bigbadevilaussie-hue/Fan-Mate/WebServer.cpp

#include "WebServer.h"
#include "WiFiManager.h"
#include "FanController.h"
#include "Logging.h"
#include "Settings.h"
#include "OpalClient.h"
#include "AutoBoost.h"
#include "Config.h"
#include "WebPage.h"
#include "SerialBuffer.h"

#include <WebServer.h>
#include <ESPmDNS.h>
#include <LittleFS.h>
#include <Update.h>
#include <ArduinoJson.h>
#include <time.h>
#include <sys/time.h>

extern int  kill_get_state();
extern void kill_request_clear();
extern void kill_request_auto();

static WebServer server(HTTP_PORT);

extern volatile bool otaInProgress;
static bool otaStarted = false;
static unsigned long host_last_ms = 0;

static void note_host() { host_last_ms = millis(); }

static void handle_serial_page() {
    String html = R"rawliteral(
<!DOCTYPE html><html><head><meta charset="utf-8">
<title>Fan-Mate Serial</title>
<style>
html,body{margin:0;padding:0;height:100%;overflow:hidden}
body{font-family:ui-monospace,monospace;background:#181825;color:#cdd6f4;font-size:13px}
#log{background:#181825;padding:6px;height:100%;overflow-y:auto;white-space:pre-wrap;word-break:break-all;box-sizing:border-box}
</style>
<script>
function refresh(){
  fetch('/serial-raw')
    .then(r=>r.text())
    .then(t=>{
      const el=document.getElementById('log');
      const at_bottom = el.scrollHeight - el.scrollTop - el.clientHeight < 50;
      el.textContent = t;
      if(at_bottom) el.scrollTop = el.scrollHeight;
    });
}
setInterval(refresh, 2000);
window.onload = refresh;
</script>
</head><body>
<div id="log">loading...</div>
</body></html>
)rawliteral";
    server.send(200, "text/html", html);
}

static void handle_serial_raw() {
    server.send(200, "text/plain", get_serial_dump());
}

static void handle_root() {
    note_host();
    server.send_P(200, "text/html", INDEX_HTML);
}

static void handle_status() {
    note_host();
    extern float currentTemp;
    extern int   fanPct;
    extern int   fanRPM;
    extern int   alertState;
    extern bool  phonePresent;
    extern float lastNetKbps;
    extern bool  fan_stall_active();

    String json = "{";
    json += "\"fw\":\"" + String(FAN_MATE_VERSION) + "\",";
    json += "\"uptime\":" + String(millis() / 1000) + ",";
    json += "\"ip\":\"" + wifi_ip() + "\",";
    json += "\"rssi\":" + String(wifi_rssi()) + ",";
    json += "\"ssid\":\"" + wifi_ssid_connected() + "\",";
    json += "\"temp\":" + String(currentTemp, 2) + ",";
    json += "\"fan\":" + String(fanPct) + ",";
    json += "\"rpm\":" + String(fanRPM) + ",";
    json += "\"phone\":" + String(phonePresent ? 1 : 0) + ",";
    json += "\"alert\":" + String(alertState) + ",";
    json += "\"fan_stall\":" + String(fan_stall_active() ? 1 : 0) + ",";
    int boostGear = auto_boost_data_gear();
    json += "\"boost\":" + String(boostGear > 0 ? 1 : 0) + ",";
    json += "\"boost_lvl\":" + String(boostGear) + ",";
    json += "\"cooling\":" + String(auto_boost_cooling() ? 1 : 0) + ",";
    json += "\"net_kbps\":" + String(lastNetKbps, 1) + ",";
    // Read the actual heat gear state (stateful, matches the fan decision)
    extern int heat_get_gear();
    json += "\"temp_lvl\":" + String(heat_get_gear()) + ",";
    json += "\"opal\":" + String(opal_logged_in() ? 1 : 0) + ",";
    unsigned long since_host = (host_last_ms > 0) ? (millis() - host_last_ms) : 999999;
    int host_alive = (since_host < 60000) ? 1 : 0;
    json += "\"host\":" + String(host_alive) + ",";
    json += "\"host_last_seen\":" + String(since_host / 1000) + ",";
    json += "\"sleep\":" + String(sys_state == STATE_LIGHT_SLEEP ? 1 : 0) + ",";
    json += "\"sleep_countdown\":0,";
    json += "\"log_size\":" + String(log_get_size()) + ",";

    extern float weather_get_temp();
    extern float readNTC();
    json += "\"outdoor_c\":" + String(weather_get_temp(), 1) + ",";
    json += "\"room_c\":" + String(readNTC(), 1) + ",";

    extern float webTempHist[];
    extern float webNetHist[];
    extern int   webHistIdx;

    json += "\"temp_hist\":[";
    for (int i = 0; i < 60; i++) {
        int idx = (webHistIdx + i) % 60;
        if (i > 0) json += ",";
        json += String(webTempHist[idx], 1);
    }
    json += "],";

    json += "\"net_hist\":[";
    for (int i = 0; i < 60; i++) {
        int idx = (webHistIdx + i) % 60;
        if (i > 0) json += ",";
        json += String(webNetHist[idx], 1);
    }
    json += "],";

    extern float webRpmHist[];
    json += "\"rpm_hist\":[";
    for (int i = 0; i < 60; i++) {
        int idx = (webHistIdx + i) % 60;
        if (i > 0) json += ",";
        json += String((int)webRpmHist[idx]);
    }
    json += "],";

    json += "\"kill_mode\":" + String(kill_get_state()) + ",";
    json += "\"temp_gear1\":" + String(config.tempGear1, 1) + ",";
    json += "\"temp_gear2\":" + String(config.tempGear2, 1) + ",";
    json += "\"temp_gear3\":" + String(config.tempGear3, 1) + ",";
    json += "\"temp_gear4\":" + String(config.tempGear4, 1) + ",";
    json += "\"temp_warning\":" + String(config.tempGear2, 1) + ",";
    json += "\"delta_trigger\":" + String(config.deltaTrigger, 1) + ",";
    json += "\"temp_panic\":" + String(config.tempGear3, 1) + ",";
    json += "\"temp_kill\":" + String(config.tempGear4, 1) + ",";
    json += "\"boost_threshold\":" + String(config.boostThreshold);

    json += "}";

    server.send(200, "application/json", json);
}

static void handle_config_get() {
    String json = "{";

    json += "\"temp\":{";
    json += "\"gear1\":" + String(config.tempGear1, 1) + ",";
    json += "\"gear2\":" + String(config.tempGear2, 1) + ",";
    json += "\"gear3\":" + String(config.tempGear3, 1) + ",";
    json += "\"gear4\":" + String(config.tempGear4, 1) + ",";
    json += "\"hysteresis\":" + String(config.tempHysteresis, 1) + ",";
    json += "\"delta_trigger\":" + String(config.deltaTrigger, 1);
    json += "},";

    json += "\"boost\":{";
    json += "\"threshold\":" + String(config.boostThreshold) + ",";
    json += "\"on_hold\":" + String(config.boostOnHold) + ",";
    json += "\"off_hold\":" + String(config.boostOffHold);
    json += "}";

    json += "}";
    server.send(200, "application/json", json);
}

static void handle_config_post() {
    note_host();
    if (!server.hasArg("plain")) {
        server.send(400, "text/plain", "no body");
        return;
    }

    String body = server.arg("plain");
    Serial.printf("[HTTP] POST /config: %s\n", body.c_str());

    StaticJsonDocument<512> check;
    if (deserializeJson(check, body) != DeserializationError::Ok) {
        server.send(400, "text/plain", "bad json");
        return;
    }

    // v4.31b: respond immediately. settings_apply_json() runs the seal +
    // config snapshot + two Drive uploads, which can take 10-20 seconds.
    // Blocking on those starves the WebServer and times out the client.
    server.send(200, "text/plain", "OK");
    delay(20);

    settings_apply_json(body.c_str());
}

static void handle_time_post() {
    note_host();
    if (!server.hasArg("plain")) {
        server.send(400, "text/plain", "no body");
        return;
    }

    String body = server.arg("plain");
    StaticJsonDocument<128> doc;
    DeserializationError err = deserializeJson(doc, body);
    if (err) {
        server.send(400, "text/plain", "bad json");
        return;
    }

    uint32_t epoch = doc["epoch"] | 0;
    if (epoch < 1700000000UL || epoch > 4102444800UL) {
        server.send(400, "text/plain", "bad epoch");
        return;
    }

    struct timeval tv;
    tv.tv_sec  = epoch;
    tv.tv_usec = 0;
    settimeofday(&tv, nullptr);
    setenv("TZ", "AEST-10", 1);
    tzset();

    Serial.printf("[TIME] synced: %lu\n", (unsigned long)epoch);
    server.send(200, "text/plain", "OK");
}

static void handle_log_download() {
    note_host();
    if (!LittleFS.exists("/log.csv")) {
        server.send(404, "text/plain", "no log");
        return;
    }

    File f = LittleFS.open("/log.csv", "r");
    if (!f) {
        server.send(500, "text/plain", "open failed");
        return;
    }

    server.streamFile(f, "text/csv");
    f.close();
}

static void handle_log_info() {
    note_host();
    String json = "{";
    json += "\"size\":" + String(log_get_size()) + ",";
    json += "\"sealed_count\":" + String(log_sealed_count()) + ",";
    json += "\"sealed_bytes\":" + String(log_sealed_bytes()) + ",";
    json += "\"free_bytes\":" + String(LittleFS.totalBytes() - LittleFS.usedBytes()) + ",";
    json += "\"paused\":" + String(log_rotation_paused() ? 1 : 0);
    json += "}";
    server.send(200, "application/json", json);
}

static void handle_log_clear() {
    note_host();
    log_clear();
    server.send(200, "text/plain", "cleared");
}

static void handle_ota_upload() {
    HTTPUpload& upload = server.upload();
    static uint32_t ota_total = 0;
    static uint32_t ota_last_print = 0;

    if (upload.status == UPLOAD_FILE_START) {
        log_print("[OTA] start: %s\n", upload.filename.c_str());
        otaInProgress = true;
        otaStarted = true;
        ota_total = 0;
        ota_last_print = 0;

        if (!Update.begin(UPDATE_SIZE_UNKNOWN)) {
            log_print("[OTA] begin FAILED: %s\n", Update.errorString());
            otaStarted = false;
        }
    } else if (upload.status == UPLOAD_FILE_WRITE) {
        if (otaStarted) {
            if (Update.write(upload.buf, upload.currentSize) != upload.currentSize) {
                log_print("[OTA] write FAILED: %s\n", Update.errorString());
                otaStarted = false;
            } else {
                ota_total += upload.currentSize;
                // print every 128 KB
                if (ota_total - ota_last_print >= 131072) {
                    ota_last_print = ota_total;
                    log_print("[OTA] downloading %u KB\n",
                              (unsigned)(ota_total / 1024));
                }
            }
        }
    } else if (upload.status == UPLOAD_FILE_END) {
        if (otaStarted) {
            if (Update.end(true)) {
                log_print("[OTA] done: %u bytes, rebooting\n", upload.totalSize);
            } else {
                log_print("[OTA] end FAILED: %s\n", Update.errorString());
            }
        }
    }
}

static void handle_ota_done() {
    if (Update.hasError()) {
        otaInProgress = false;
        server.send(500, "text/plain",
                    "FAIL: " + String(Update.errorString()));
    } else {
        log_write_event("OTA");
        server.send(200, "text/plain", "OK, rebooting");
        delay(500);
        ESP.restart();
    }
}

static void handle_reboot() {
    note_host();
    log_write_event("REBOOT");
    server.send(200, "text/plain", "Rebooting...");
    delay(500);
    ESP.restart();
}

extern size_t log_list_sealed(char names[][48], size_t max);
extern bool   log_delete_sealed(const char* name);

static void handle_log_list() {
    note_host();
    char names[32][48];
    size_t n = log_list_sealed(names, 32);

    String json = "[";
    for (size_t i = 0; i < n; i++) {
        char p[80];
        snprintf(p, sizeof(p), "/%s", names[i]);
        File f = LittleFS.open(p, "r");
        size_t sz = 0;
        uint32_t crc = 0xFFFFFFFF;
        if (f) {
            sz = f.size();
            uint8_t buf[256];
            while (f.available()) {
                size_t r = f.read(buf, sizeof(buf));
                for (size_t j = 0; j < r; j++) {
                    crc ^= buf[j];
                    for (int k = 0; k < 8; k++)
                        crc = (crc >> 1) ^ (0xEDB88320 & -(crc & 1));
                }
            }
            crc ^= 0xFFFFFFFF;
            f.close();
        } else {
            crc = 0;
        }
        if (i > 0) json += ",";
        char entry[128];
        snprintf(entry, sizeof(entry),
                 "{\"name\":\"%s\",\"size\":%u,\"crc\":\"%08x\"}",
                 names[i], (unsigned)sz, (unsigned)crc);
        json += entry;
    }
    json += "]";
    server.send(200, "application/json", json);
}

static void handle_log_file() {
    note_host();
    if (!server.hasArg("name")) { server.send(400, "text/plain", "no name"); return; }
    String name = server.arg("name");
    if (name.indexOf("..") >= 0 || name.indexOf("/") >= 0) {
        server.send(400, "text/plain", "bad name"); return;
    }
    String path = "/" + name;
    if (!LittleFS.exists(path)) { server.send(404, "text/plain", "not found"); return; }
    File f = LittleFS.open(path, "r");
    if (!f) { server.send(500, "text/plain", "open failed"); return; }
    server.streamFile(f, "text/csv");
    f.close();
}

static void handle_log_ack() {
    note_host();
    if (!server.hasArg("plain")) { server.send(400, "text/plain", "no body"); return; }
    StaticJsonDocument<256> doc;
    if (deserializeJson(doc, server.arg("plain"))) {
        server.send(400, "text/plain", "bad json"); return;
    }
    const char* name = doc["name"] | "";
    if (name[0] == 0) { server.send(400, "text/plain", "no name"); return; }
    bool ok = log_delete_sealed(name);
    if (ok) {
        char ev[80];
        snprintf(ev, sizeof(ev), "UPLOAD,%s,OK", name);
        log_write_event(ev);
    }
    server.send(200, "text/plain", "OK");
}

static void handle_log_nack() {
    note_host();
    if (!server.hasArg("plain")) { server.send(400, "text/plain", "no body"); return; }
    StaticJsonDocument<256> doc;
    if (deserializeJson(doc, server.arg("plain"))) {
        server.send(400, "text/plain", "bad json"); return;
    }
    const char* name = doc["name"] | "";
    const char* reason = doc["reason"] | "unknown";
    if (name[0] == 0) { server.send(400, "text/plain", "no name"); return; }
    char ev[96];
    snprintf(ev, sizeof(ev), "UPLOAD,%s,NACK,%s", name, reason);
    log_write_event(ev);
    server.send(200, "text/plain", "OK");
}

static void handle_kill_clear() {
    note_host();
    kill_request_clear();
    server.send(200, "text/plain", "OK");
}

static void handle_kill_auto() {
    note_host();
    kill_request_auto();
    server.send(200, "text/plain", "OK");
}

static void handle_boost_gear() {
    int n = server.arg("n").toInt();
    extern float currentTemp;
    auto_boost_force_gear(n, currentTemp);
    server.send(200, "text/plain", "gear=" + String(n));
}

void server_setup() {
    if (!wifi_connected()) {
        Serial.println("[HTTP] WiFi not connected — server not started");
        return;
    }

    server.on("/",           HTTP_GET,  handle_root);
    server.on("/status",     HTTP_GET,  handle_status);
    server.on("/config",     HTTP_GET,  handle_config_get);
    server.on("/config",     HTTP_POST, handle_config_post);
    server.on("/time",       HTTP_POST, handle_time_post);
    server.on("/log.csv",    HTTP_GET,  handle_log_download);
    server.on("/log/info",   HTTP_GET,  handle_log_info);
    server.on("/log/clear",  HTTP_POST, handle_log_clear);
    server.on("/log/list",   HTTP_GET,  handle_log_list);
    server.on("/log/file",   HTTP_GET,  handle_log_file);
    server.on("/log/ack",    HTTP_POST, handle_log_ack);
    server.on("/log/nack",   HTTP_POST, handle_log_nack);
    server.on("/serial",     HTTP_GET,  handle_serial_page);
    server.on("/serial-raw", HTTP_GET,  handle_serial_raw);
    server.on("/kill/clear",  HTTP_POST, handle_kill_clear);
    server.on("/boost/gear",  HTTP_GET,  handle_boost_gear);
    server.on("/kill/auto",   HTTP_POST, handle_kill_auto);
    server.on("/reboot",     HTTP_GET,  handle_reboot);
    server.on("/ota",        HTTP_POST, handle_ota_done, handle_ota_upload);

    server.onNotFound([]() {
        server.send(404, "text/plain", "404");
    });

    server.begin();

    log_print("[HTTP] server started on port %d\n", HTTP_PORT);
    log_print("[HTTP] http://%s/\n", wifi_mdns_name().c_str());
    log_print("[HTTP] http://%s/\n", wifi_ip().c_str());
}

void server_loop() {
    server.handleClient();
}

String server_version() {
    return String(FAN_MATE_VERSION);
}
