bigbadevilaussie-hue/Fan-Mate/Settings.h

#ifndef SETTINGS_H
#define SETTINGS_H

#include <Arduino.h>

// ============================================================
//  Fan-Mate runtime configuration
//  V4.20 — schema:
//    temp  : gear1/gear2/gear3/gear4 + hysteresis
//    boost : mode + normal/aggr profiles (nested)
// ============================================================

struct FanMateConfig {
    // Heat control (four gear thresholds, 30/32/34/36 by default)
    float   tempGear1;   // Warm     -> gear 1
    float   tempGear2;   // Hot      -> gear 2
    float   tempGear3;   // Hotter   -> gear 3
    float   tempGear4;   // Critical -> gear 4 + kill
    float   tempHysteresis;
    float   deltaTrigger;  // phone-room delta that fires the guard (default 5.1)


    // Boost (single profile, always active)
    int     boostThreshold;   // KB/s
    int     boostOnHold;      // ticks over threshold to bump gear
    int     boostOffHold;     // ticks under threshold to drop gear
};

extern FanMateConfig config;

void settings_load();
void settings_save();
void settings_reset();
void settings_apply_json(const char* json);

#endif
