bigbadevilaussie-hue/Fan-Mate/secrets.example.h

#ifndef SECRETS_H
#define SECRETS_H

// ============================================================
//  Fan-Mate V3.00 — example credentials
//
//  Copy this file to secrets.h and fill in your real values:
//      cp secrets.example.h secrets.h
//
//  secrets.h is gitignored and will never be pushed.
// ============================================================

// WiFi network
#define WIFI_SSID       "your-wifi-name"
#define WIFI_PASSWORD   "your-wifi-password"

// mDNS hostname
#define MDNS_HOSTNAME   "fan-mate"

// Opal router API
#define OPAL_IP         "192.168.8.1"
#define OPAL_USER       "root"
#define OPAL_PASSWORD   "your-router-password"

#endif

// Google Drive upload endpoint (Apps Script web app URL)
// Keep secret — anyone with this URL can write to your Drive.
#define DRIVE_URL "https://script.google.com/macros/s/YOUR_DEPLOYMENT_ID/exec"
